H4w4k4/LNA_1MHz/Measures/LNA_+80dB_BW100kHz.csv

#Digilent WaveForms Network Analyzer - Bode
#Device Name: Discovery3
#Date Time: 2024-02-08 19:11:51.942
#Start: 1 Hz
#Stop: 2e+06 Hz
#Steps: 151
#Wavegen: Wavegen C1
#Amplification: 1 X
#Settle: 10 ms
#MinPeriods: 32
#Channel: Channel 2
#Range: 5.13569 V
#Offset: 8.29643e-05 V
#Relative: yes
Frequency (Hz) | Channel 2 Magnitude (dB) | Channel 2 Phase (deg)
1.000000000000002 | -43.96483877176244 | -5.575643654026678
1.101556726136675 | -42.02245147476283 | -9.611498158912578
1.213427220896945 | -39.87242357713987 | -13.87676497355594
1.336658916856357 | -37.49145982058762 | -18.71513439624876
1.472405620413677 | -34.80023567364334 | -24.41389408864443
1.621938314768127 | -32.02305053411627 | -30.23440827058212
1.786657060011607 | -29.0950523972157 | -36.59720314852787
1.968104101755354 | -26.07478936769422 | -43.06398704273482
2.167978311025786 | -23.0317108700336 | -49.83632005712772
2.388151090628878 | -19.98065341663706 | -56.85179840313646
2.630683896912867 | -16.9247157678282 | -64.23453408683054
2.897847540983796 | -13.84611106742463 | -72.05079832417465
3.192143450089312 | -10.85314752471614 | -80.22962180516166
3.516327088239006 | -7.885047240252582 | -88.9310045359733
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
