H4w4k4/LNA_1MHz/Measures/LNA_+80dB_BW1MHz.csv

#Digilent WaveForms Network Analyzer - Bode
#Device Name: Discovery3
#Date Time: 2024-02-08 19:35:23.243
#Start: 1 Hz
#Stop: 2e+06 Hz
#Steps: 151
#Wavegen: Wavegen C1
#Amplification: 1 X
#Settle: 10 ms
#MinPeriods: 32
#Channel: Channel 2
#Range: 5.13569 V
#Offset: 8.29643e-05 V
#Relative: yes
Frequency (Hz) | Channel 2 Magnitude (dB) | Channel 2 Phase (deg)
1.000000000000002 | -43.79014581233968 | -5.419648488701091
1.101556726136675 | -41.92888878441256 | -8.70554509133564
1.213427220896945 | -39.82343436971784 | -13.12117107521072
1.336658916856357 | -37.36078501579866 | -18.65423402042464
1.472405620413677 | -34.79103967583062 | -24.34528284160012
1.621938314768127 | -31.96300603086023 | -30.44228863532531
1.786657060011607 | -29.05568614232046 | -36.50510968612254
1.968104101755354 | -26.05712497237884 | -43.04586566451667
2.167978311025786 | -23.00178252935245 | -49.83157726886405
2.388151090628878 | -19.92995563275706 | -56.93682104255758
2.630683896912867 | -16.86206433432692 | -64.29565299729582
2.897847540983796 | -13.82173892975795 | -72.08646709493155
3.192143450089312 | -10.79567761033734 | -80.36629989339033
3.516327088239006 | -7.833001811461884 | -89.08598166381525
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
