H4w4k4/LNA_1MHz/LTSpice/LNA_1MHz.asc

C1: cap; 4µ7
C2: cap; 4µ7
C3: cap; 120pF
C4: cap; 100pF
C5: cap; 150pF
C6: cap; 22pF
C7: cap; 700µF
C8: cap; 1200pF
C9: cap; 1000pF
C10: cap; 1500pF
C11: cap; 220pF
C12: cap; 700µF
C13: cap; 700µF
C14: cap; 300pF
C15: cap; 300pF
C16: cap; 22pF
C17: cap; 330µF
C18: cap; 300pF
C19: cap; 300pF
C20: cap; 22pF
C21: cap; 330µF
C22: cap; 300pF
C23: cap; 300pF
C24: cap; 22pF
C25: cap; 330µF
C26: cap; 300pF
C27: cap; 300pF
C28: cap; 22pF
C29: cap; 330µF
C30: cap; 680µF
C31: cap; 300pF
C32: cap; 300pF
C33: cap; 22pF
C34: cap; 330µF
C35: cap; 4µ7
C36: cap; 4µ7
C37: cap; 120pF
C38: cap; 100pF
C39: cap; 150pF
C40: cap; 22pF
C41: cap; 700µF
Q1: npn; BCW60A
Q2: npn; BCW60A
Q3: npn; BCW60A
Q4: npn; BCW60A
Q5: npn; BCW60A
Q6: npn; BCW60A
Q7: npn; BCW60A
Q8: npn; BCW60A
Q9: npn; BCW60A
Q10: npn; BCW60A
Q11: npn; BCW60A
Q12: npn; BCW60A
Q13: npn; BCW60A
Q14: npn; BCW60A
Q15: npn; BCW60A
Q16: npn; BCW60A
Q17: npn; BCW60A
Q18: npn; BCW60A
Q19: npn; BCW60A
Q20: npn; BCW60A
R1: res; 511
R2: res; 2k
R3: res; 5k76
R4: res; 100
R5: res; 2k
R6: res; 1k69
R7: res; 1k24
R8: res; 4k02
R9: res; 2k15
R10: res; 49.9
R11: res; 1k69
R12: res; 1k24
R13: res; 4k02
R14: res; 2k15
R15: res; 49.9
R16: res; 49.9
R17: res; 4k02
R18: res; 4k02
R19: res; 4k02
R20: res; 499
R21: res; 499
R22: res; 100
R23: res; 249
R24: res; 10
R25: res; 4k02
R26: res; 4k02
R27: res; 4k02
R28: res; 4k02
R29: res; 499
R30: res; 499
R31: res; 100
R32: res; 249
R33: res; 10
R34: res; 4k02
R35: res; 4k02
R36: res; 4k02
R37: res; 4k02
R38: res; 499
R39: res; 499
R40: res; 100
R41: res; 249
R42: res; 10
R43: res; 4k02
R44: res; 4k02
R45: res; 4k02
R46: res; 4k02
R47: res; 499
R48: res; 499
R49: res; 100
R50: res; 249
R51: res; 10
R52: res; 4k02
R53: res; 499
R54: res; 4k02
R55: res; 4k02
R56: res; 4k02
R57: res; 499
R58: res; 499
R59: res; 100
R60: res; 249
R61: res; 10
R62: res; 4k02
R63: res; 1Meg
R64: res; 511
R65: res; 2k
R66: res; 5k76
R67: res; 100
R68: res; 2k
R69: res; 1k69
R70: res; 1k24
R71: res; 4k02
R72: res; 2k15
R73: res; 49.9
U1: LT6232
U2: LT6232
U3: LT6232
U4: LT6232
U5: LT1365
U6: LT1365
U7: LT1365
U8: LT1365
U9: LT1818
U10: LT1818
U11: LT1818
U12: LT1818
U13: LT1818
U14: LT6232
U15: LT6232
U16: LT6232
U17: LT6232
U18: LT1365
V1: voltage; 5
V2: voltage; 5
V3: voltage; SINE(0 1u 10k); AC 1u
Named nets: 0, VDD, VSS, Out_1MegHz, Out_100kHz, Out_Full, IN1, OUT_inStage, IN, Out_1MegHz1
.ac dec 100 100m 30meg
